janzavorka/BP_PROJ/BAP/zaverecna_prace_FEL/main.tex

\documentclass[12pt,a4paper,twoside]{article}

%%% Packages %%%
\renewcommand{\baselinestretch}{1.0} % Change to 1.65 for double spacing

% text area 15.5cm x 23.7cm
\usepackage[a4paper,top=3.0cm,bottom=3.0cm,left=3.0cm,right=2.5cm]{geometry}

%\usepackage{natbib}
\clubpenalty 10000  %kontrolovat sirotky
\widowpenalty 10000 %kontrolovat vdovy
%\tolerance=1
%\emergencystretch=\maxdimen
%\hyphenpenalty=5000
%\hbadness=5000

%\usepackage{acro}
\usepackage[acronym,section=section]{glossaries}
\usepackage{caption}
\usepackage{subcaption}
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
  frame=single,	                   % adds a frame around the code
  keepspaces=true,                 % keeps spaces in text, useful for keeping indentation of code (possibly needs columns=flexible)
  keywordstyle=\color{blue},       % keyword style
  language=C,                 % the language of the code
  morekeywords={*,...},            % if you want to add more keywords to the set
  numbers=left,                    % where to put the line-numbers; possible values are (none, left, right)
  numbersep=5pt,                   % how far the line-numbers are from the code
  numberstyle=\tiny\color{mygray}, % the style that is used for the line-numbers
  rulecolor=\color{black},         % if not set, the frame-color may be changed on line-breaks within not-black text (e.g. comments (green here))
  showspaces=false,                % show spaces everywhere adding particular underscores; it overrides 'showstringspaces'
  showstringspaces=false,          % underline spaces within strings only
  showtabs=false,                  % show tabs within strings adding particular underscores
  stepnumber=2,                    % the step between two line-numbers. If it's 1, each line will be numbered
  stringstyle=\color{mymauve},     % string literal style
  tabsize=2,	                   % sets default tabsize to 2 spaces
  title=\lstname                   % show the filename of files included with \lstinputlisting; also try caption instead of title
}

%% language C colored
\lstdefinestyle{customc}{
  belowcaptionskip=1\baselineskip,
  breaklines=true,
  frame=N,
  xleftmargin=\parindent,
  language=C,
  showstringspaces=false,
  basicstyle=\footnotesize\ttfamily,
  keywordstyle=\bfseries\color{green!40!black},
  commentstyle=\itshape\color{purple!40!black},
  identifierstyle=\color{blue},
  stringstyle=\color{orange},
    breakatwhitespace=false,
    captionpos=b,
    keepspaces=true,
    numbers=left,
    numbersep=5pt,
    showspaces=false,
    showstringspaces=false,
    showtabs=false,
    tabsize=2,
}

\lstdefinestyle{customc_config}{
  belowcaptionskip=1\baselineskip,
  breaklines=true,
  frame=single,
  xleftmargin=0pt,
  language=C,
  showstringspaces=false,
  basicstyle=\footnotesize\ttfamily,
  keywordstyle=\bfseries\color{green!40!black},
  commentstyle=\itshape\color{purple!40!black},
  identifierstyle=\color{blue},
  stringstyle=\color{orange},
    breakatwhitespace=false,
    captionpos=b,
    keepspaces=true,
    numbers=none,
   	numbersep=0pt,
    showspaces=false,
    showstringspaces=false,
    showtabs=false,
    tabsize=2,
}

%%%URL line breaks
\expandafter\def\expandafter\UrlBreaks\expandafter{\UrlBreaks%  save the current one
  \do\a\do\b\do\c\do\d\do\e\do\f\do\g\do\h\do\i\do\j%
  \do\k\do\l\do\m\do\n\do\o\do\p\do\q\do\r\do\s\do\t%
  \do\u\do\v\do\w\do\x\do\y\do\z\do\A\do\B\do\C\do\D%
  \do\E\do\F\do\G\do\H\do\I\do\J\do\K\do\L\do\M\do\N%
  \do\O\do\P\do\Q\do\R\do\S\do\T\do\U\do\V\do\W\do\X%
  \do\Y\do\Z}

%%%FLOWCHARTS settings
\input{img/flowCharts/flowChartsSettings.tex}

\parskip = 4pt	% space between paragraphs

%% apendixy
\usepackage{pdfpages}

% \renewcommand{\thefigure}{\thesection.\arabic{figure}}
% \renewcommand{\thetable}{\thesection.\arabic{table}}
% \renewcommand{\theequation}{\thesection.\arabic{equation}}

\newcommand{\blankpage}{
\newpage
\thispagestyle{empty}
\mbox{}
\newpage
}

%% Today format month, year
\newcommand{\todayMonthYear}{
\ifcase \month \or Leden\or Únor\or Březen\or %
Duben\or Květen \or Červen\or Červenec\or Srpen\or Září\or Říjen\or Listopad\or %
Prosinec\fi \ \number \year
}

\newcommand{\inProgress}{\textbf{\color{red} \Large Rozpracováno, nepublikováno !!!}}

\newcommand{\notFinished}{\textbf{\color{orange} \Large Nedokončeno, doplnit !!!}}

\input{title}
\newcommand{\Author}{Jan Závorka}
\newcommand{\Title}{Interaktivní hra využívající \\ [.2em] IoT prostředky}
\newcommand{\TitleEN}{Interactive Game Based on IoT Technology}

\input{abbrev}

\begin{document}

\TitlePage{\Author}{\Title}{\TitleEN}
%\input{title}
\clearpage
\blankpage
%%% Header Definition %%%%%%%%%%%
% \pagestyle{fancy}
% % define fancy style
% \fancyhf{}
% \lhead{\leftmark}
% \rhead{\thepage}
% \headheight 15.0pt
% % redefine plain style
% \fancypagestyle{plain}{%
% 	\fancyhf{} % clear all header and footer fields
% 	\renewcommand{\headrulewidth}{0pt}
% 	\renewcommand{\footrulewidth}{0pt}}
%%%%%%%%%%%%%%%%%%%%%%%%%%%%%%%%%

%%% Header Definition %%%%%%%%%%%
\pagestyle{fancy}
\fancyhf{}
\fancyhead[LO,RE]{\scshape\nouppercase\leftmark}
\fancyhead[RO,LE]{\thepage}

% \fancyhead[RE]{\scshape\nouppercase\leftmark}
% \fancyhead[LO]{\thepage}

%%%%%%%%%%%%%%%%%%%%%%%%%%%%%%%%%

%%% zadani %%%%%%%%%%%
\includepdf{img/zadani_prace.pdf}
\blankpage
\cleardoublepage

\input{declaration.tex}
\newpage
\input{thx.tex}
\newpage

\newpage
\input{abstract.tex}
\blankpage

\pagestyle{fancy}

%%%%%%%%%%%%%%%%%%%%%%%%%%%%%%%%%

%%% List of figures, tables, abbriviations %%%%
\pagenumbering{roman}
\tableofcontents
\blankpage
\cleardoublepage

 \listoffigures
 %\blankpage
 %\cleardoublepage

\newpage
\listoftables
 %\blankpage
 %\cleardoublepage
 \clearpage

% \printglossary[type=\acronymtype,title=Abbreviations,nonumberlist]
% \blankpage
% \cleardoublepage
%%%%%%%%%%%%%

\pagenumbering{arabic}

%\setcounter{figure}{0}
%\setcounter{table}{0}
%\setcounter{equation}{0}
\clearpage
\input{introduction}
\cleardoublepage

% \input{state-of-art}
% \cleardoublepage

%\setcounter{figure}{0}
%\setcounter{table}{0}
%\setcounter{equation}{0}
\input{chapter_01}
\cleardoublepage

%\setcounter{figure}{0}
%\setcounter{table}{0}
%\setcounter{equation}{0}
\input{chapter_02}
\cleardoublepage

%\setcounter{figure}{0}
%\setcounter{table}{0}
%\setcounter{equation}{0}
\input{chapter_03}
\cleardoublepage

%\setcounter{figure}{0}
%\setcounter{table}{0}
%\setcounter{equation}{0}
\input{chapter_04}
\blankpage
\cleardoublepage

% \bibliographystyle{ieeetr}
% \bibliography{sample}

% \include{abstract}

%\bibliographystyle{czechiso.bst}
%\bibliography{ha}

\input{reference.tex}

\input{listofsw}

\include{appendix}

\cleardoublepage
\end{document}
