janzavorka/BP_PROJ/BAP/prezentace_obhajoba/img/board.PNG

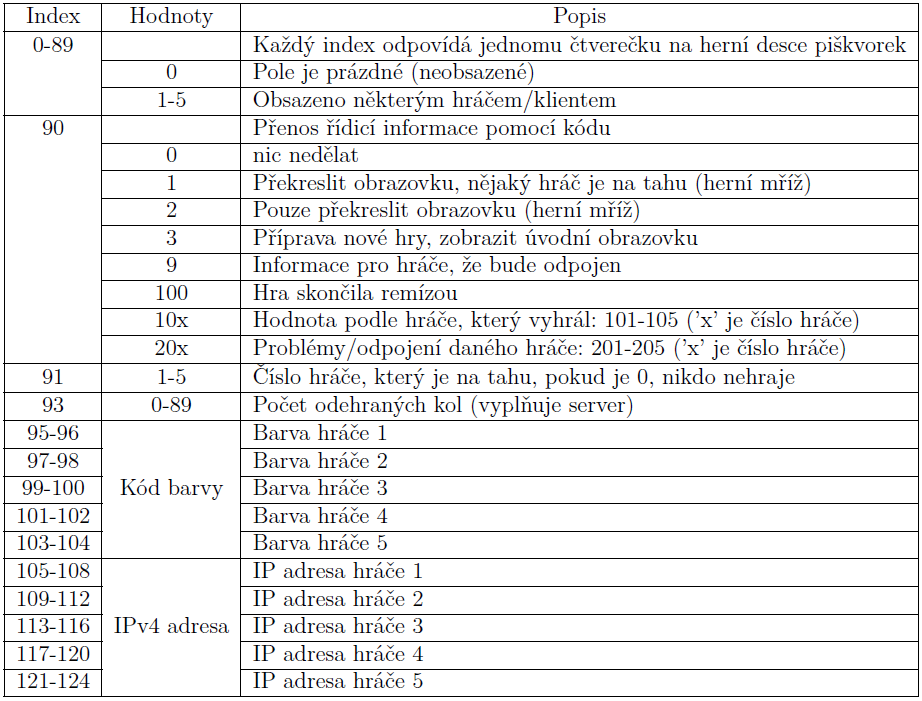
BAP/prezentace_obhajoba/img/board.PNG
