janzavorka/BP_PROJ/BAP/zaverecna_prace_FEL/img/foto/nahradni.png

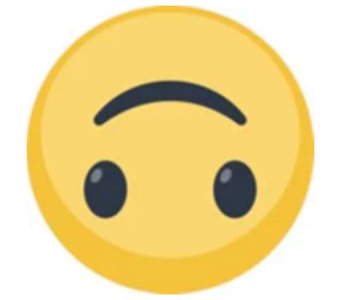
BAP/zaverecna_prace_FEL/img/foto/nahradni.png
