janzavorka/BP_PROJ/piskvorky_case/Datasheets/arduino_holes.png

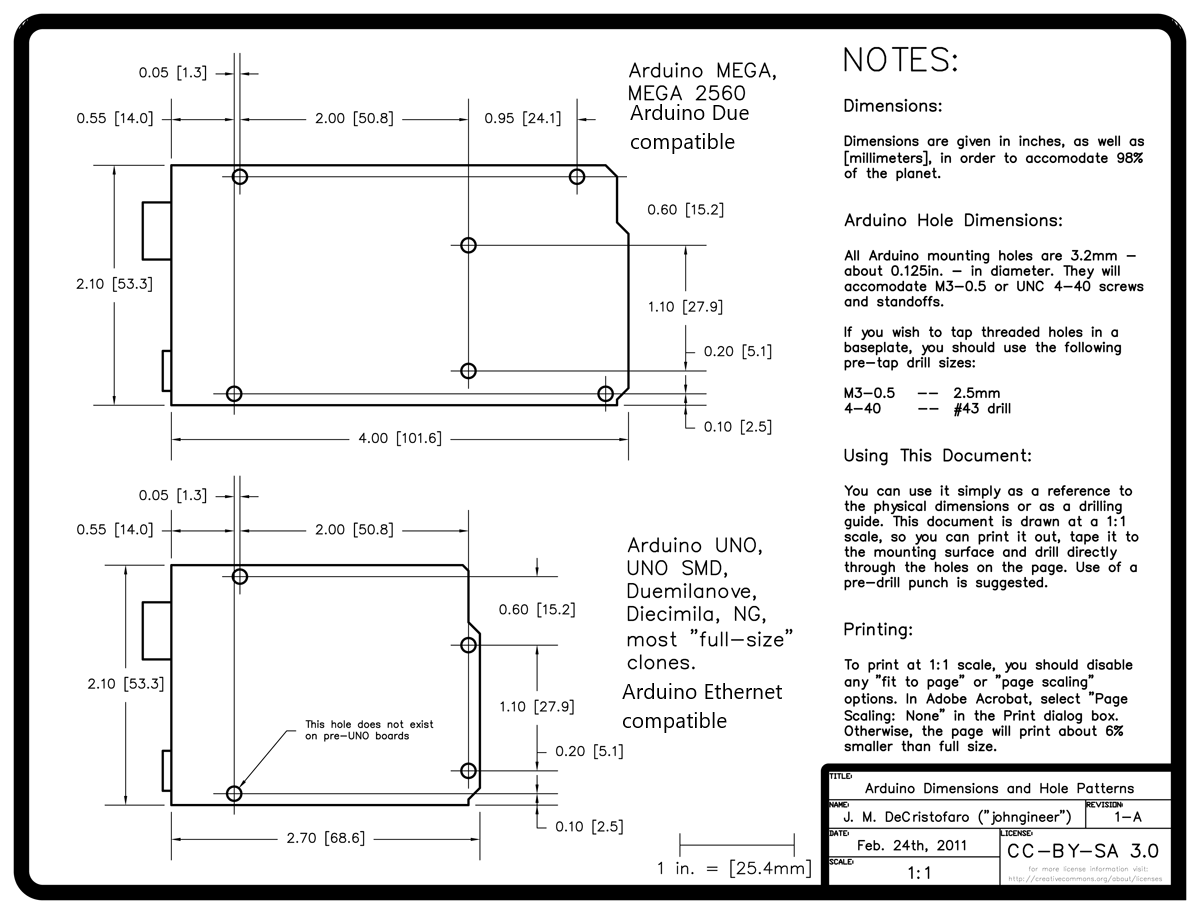
piskvorky_case/Datasheets/arduino_holes.png
